Sfeeen/PMTleech/research/memory_layouts/HY62256A.png

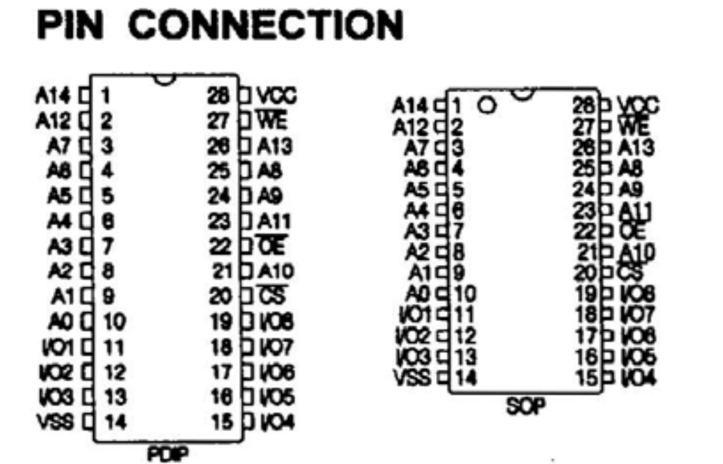
research/memory_layouts/HY62256A.png
