Sfeeen/PMTleech/research/memory_layouts/renesas_ram.png

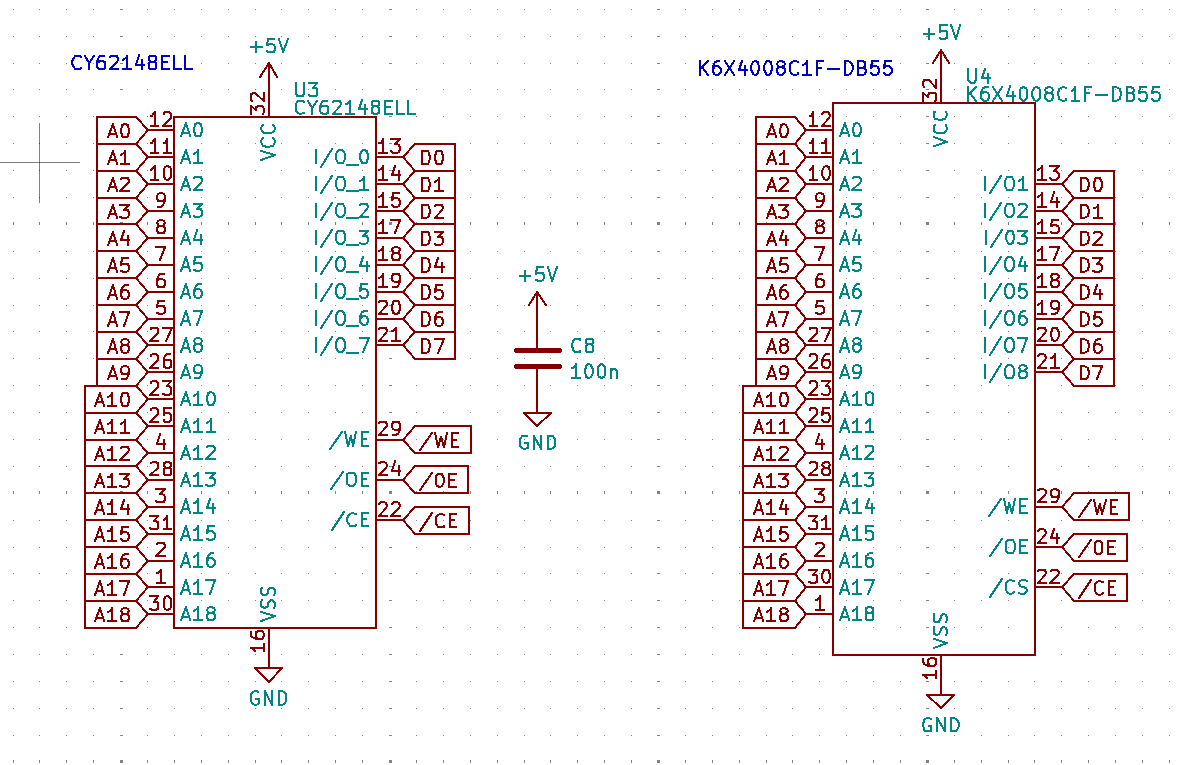
research/memory_layouts/renesas_ram.png
