Sfeeen/PMTleech/research/memory_layouts/UM6264.png

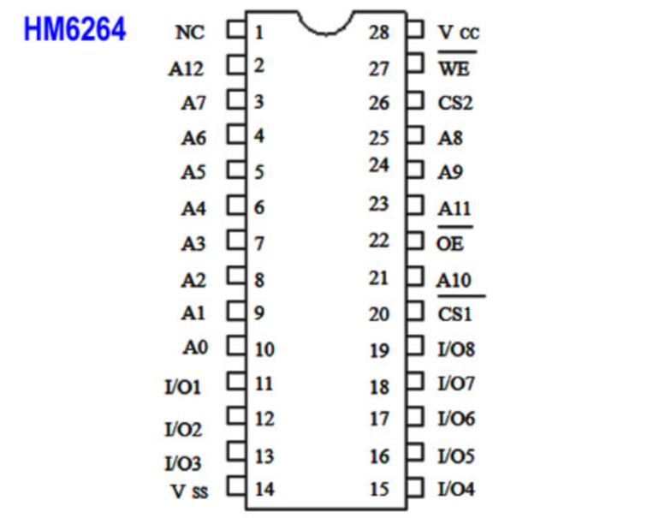
research/memory_layouts/UM6264.png
