Sfeeen/PMTleech/software_development/PC program/C/MPTleech_receiver/28chip.bmp

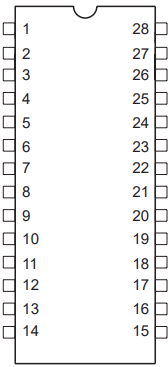
software_development/PC program/C/MPTleech_receiver/28chip.bmp
