Sfeeen/PMTleech/software_development/PC program/C/MPTleech_receiver/chip.bmp

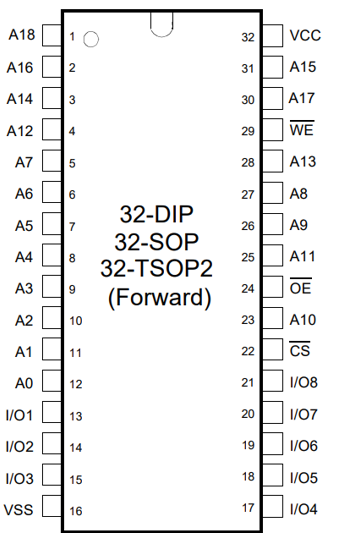
software_development/PC program/C/MPTleech_receiver/chip.bmp
