Sfeeen/PMTleech/setup_KEB.jpg

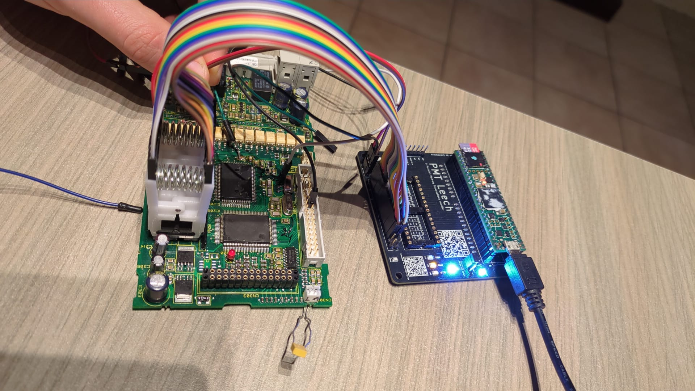
setup_KEB.jpg
